iacopoerpichini/passiveThermostatNotifier/img/gasSensor.png

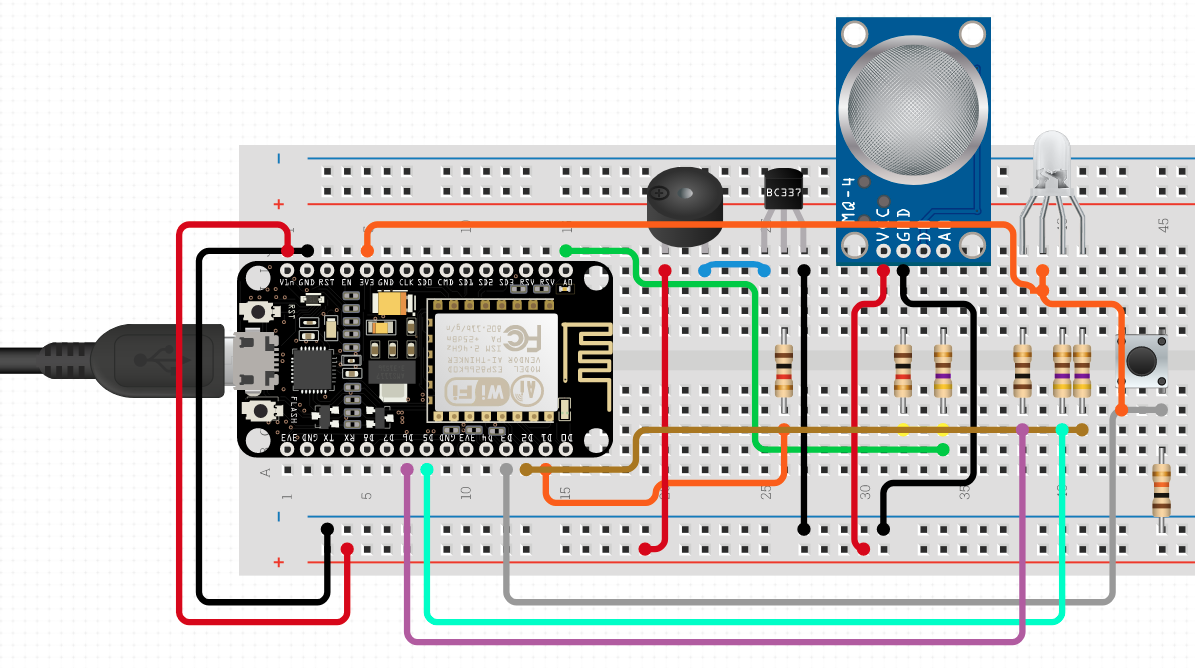
img/gasSensor.png
